richelbilderbeek/ApproxyClock/docs/photos/PiClocks.jpg

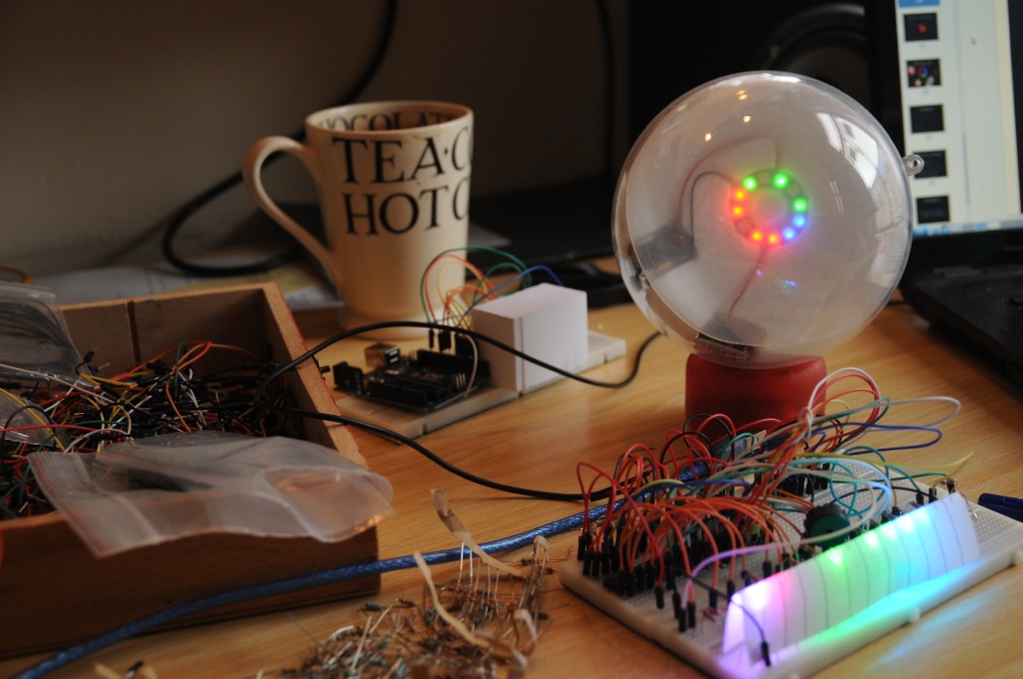
docs/photos/PiClocks.jpg
